cmmonaco/BrightSign-Smart-Interface/img/IMG_20150602_152603.jpg

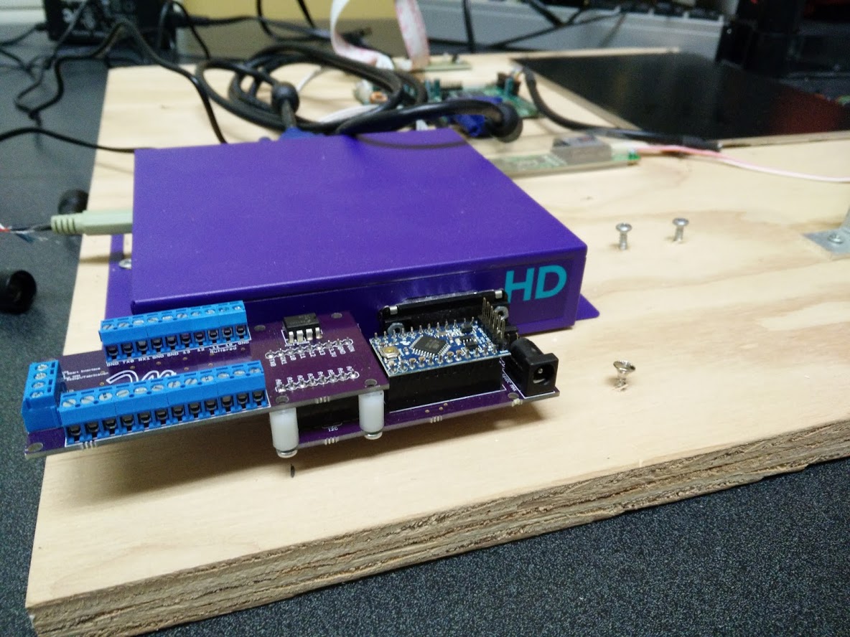
img/IMG_20150602_152603.jpg
